bkw777/FluxEngine_Kit/CASE/out/SimpleCover.jpg

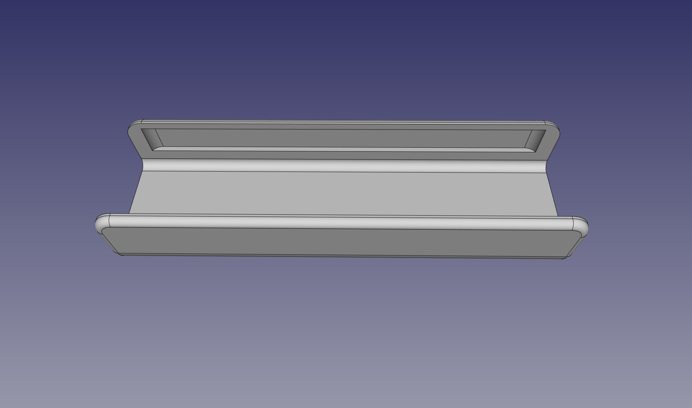
CASE/out/SimpleCover.jpg
